patrickmcm/Alevel_RFID_Card_Reader/frontend/images/dashboard/img_1.jpg

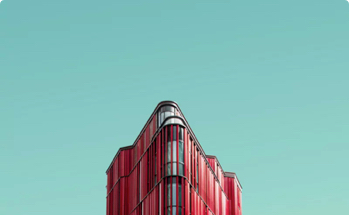
frontend/images/dashboard/img_1.jpg
