patrickmcm/Alevel_RFID_Card_Reader/frontend/images/auth/login-bg.jpg

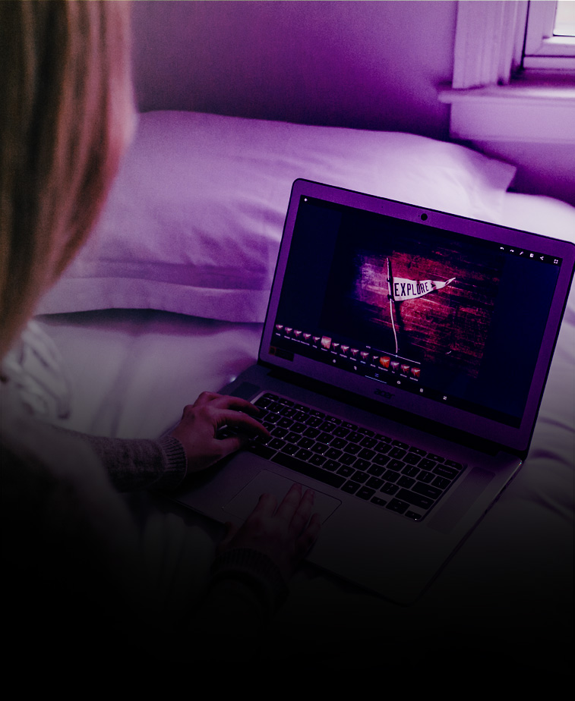
frontend/images/auth/login-bg.jpg
