patrickmcm/Alevel_RFID_Card_Reader/frontend/images/auth/lockscreen-bg.jpg

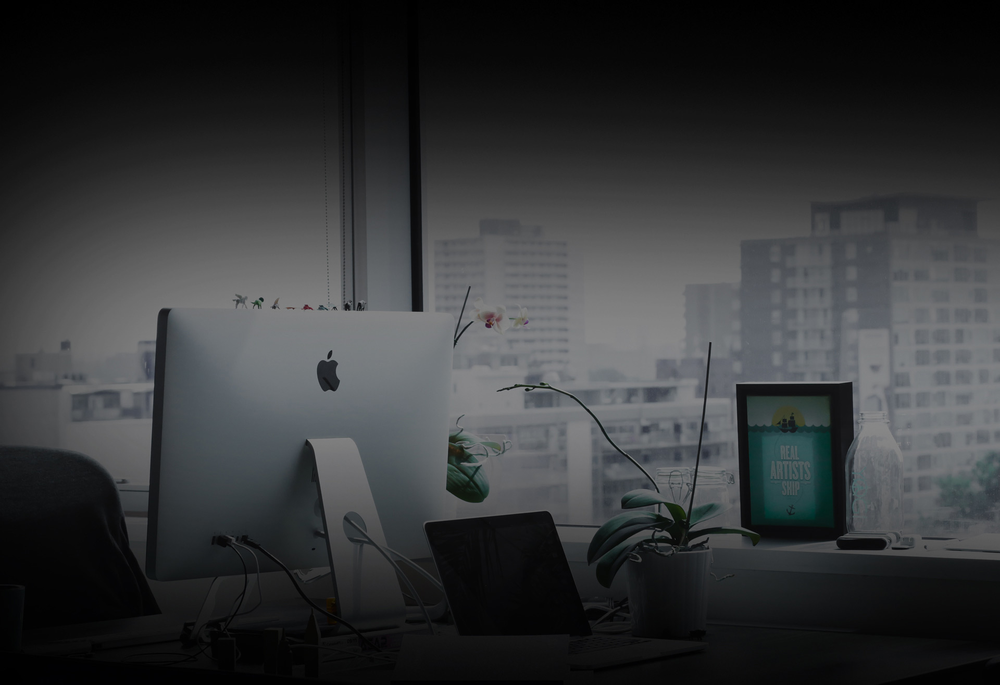
frontend/images/auth/lockscreen-bg.jpg
