patrickmcm/Alevel_RFID_Card_Reader/frontend/images/auth/register-bg.jpg

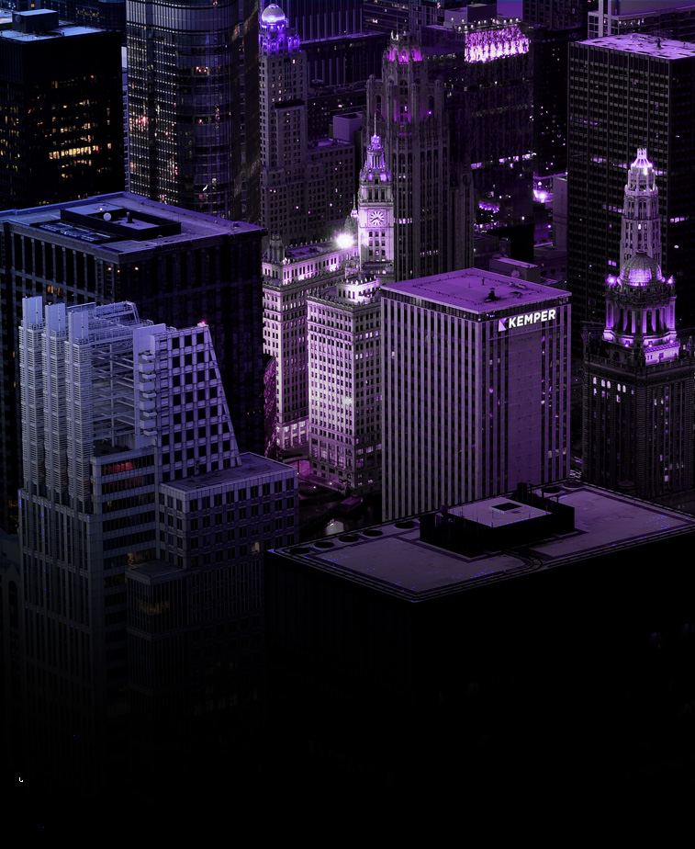
frontend/images/auth/register-bg.jpg
