patrickmcm/Alevel_RFID_Card_Reader/frontend/images/dashboard/darkBG.png

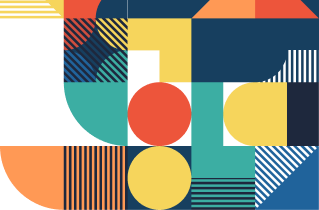
frontend/images/dashboard/darkBG.png
