patrickmcm/Alevel_RFID_Card_Reader/frontend/images/dashboard/img_2.jpg

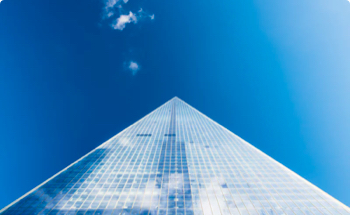
frontend/images/dashboard/img_2.jpg
