patrickmcm/Alevel_RFID_Card_Reader/frontend/images/dashboard/img_3.jpg

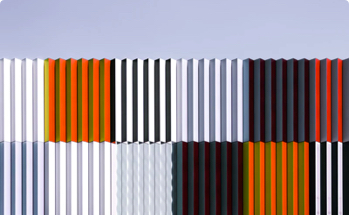
frontend/images/dashboard/img_3.jpg
