patrickmcm/Alevel_RFID_Card_Reader/frontend/images/dashboard/profile-card.jpg

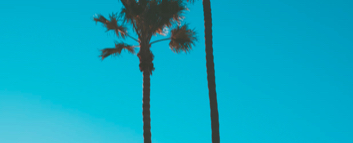
frontend/images/dashboard/profile-card.jpg
