patrickmcm/Alevel_RFID_Card_Reader/frontend/images/dashboard/progress-card-bg.jpg

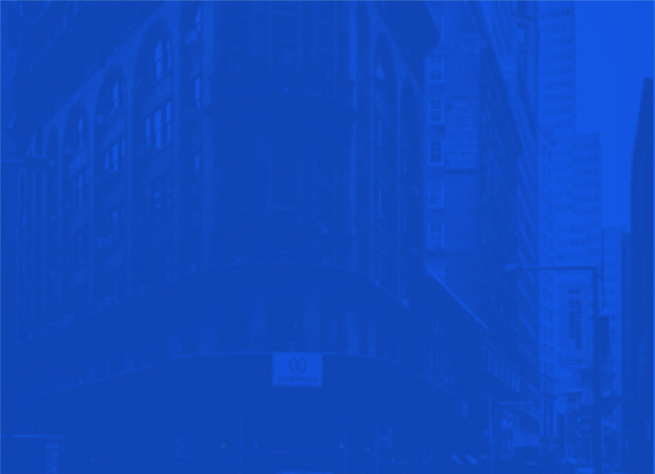
frontend/images/dashboard/progress-card-bg.jpg
