patrickmcm/Alevel_RFID_Card_Reader/frontend/images/dashboard/weather-card.jpg

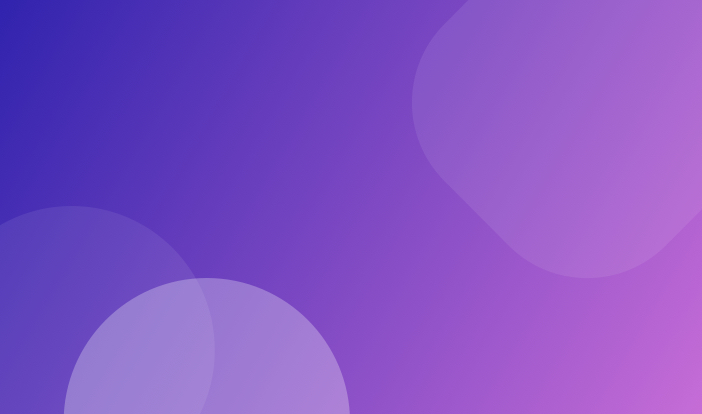
frontend/images/dashboard/weather-card.jpg
