patrickmcm/Alevel_RFID_Card_Reader/frontend/images/faces/profile/profile.jpg

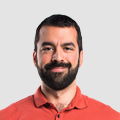
frontend/images/faces/profile/profile.jpg
