patrickmcm/Alevel_RFID_Card_Reader/frontend/images/lightbox/thumb-v-v-1.jpg

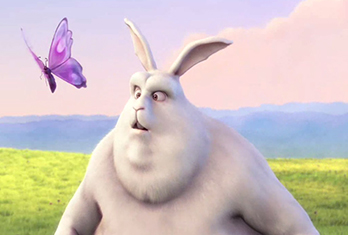
frontend/images/lightbox/thumb-v-v-1.jpg
