patrickmcm/Alevel_RFID_Card_Reader/frontend/images/lightbox/thumb-v-y-1.jpg

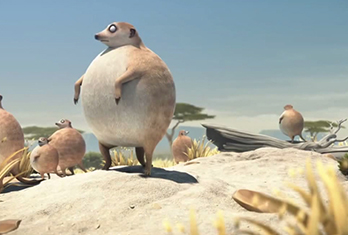
frontend/images/lightbox/thumb-v-y-1.jpg
