patrickmcm/Alevel_RFID_Card_Reader/frontend/images/lightbox/thumb-v-y-2.jpg

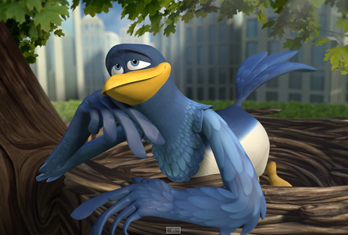
frontend/images/lightbox/thumb-v-y-2.jpg
