patrickmcm/Alevel_RFID_Card_Reader/hardware/schematic/schematic.kicad_sch

## KiCad design hardware/schematic/schematic.kicad_sch (2023-08-01)

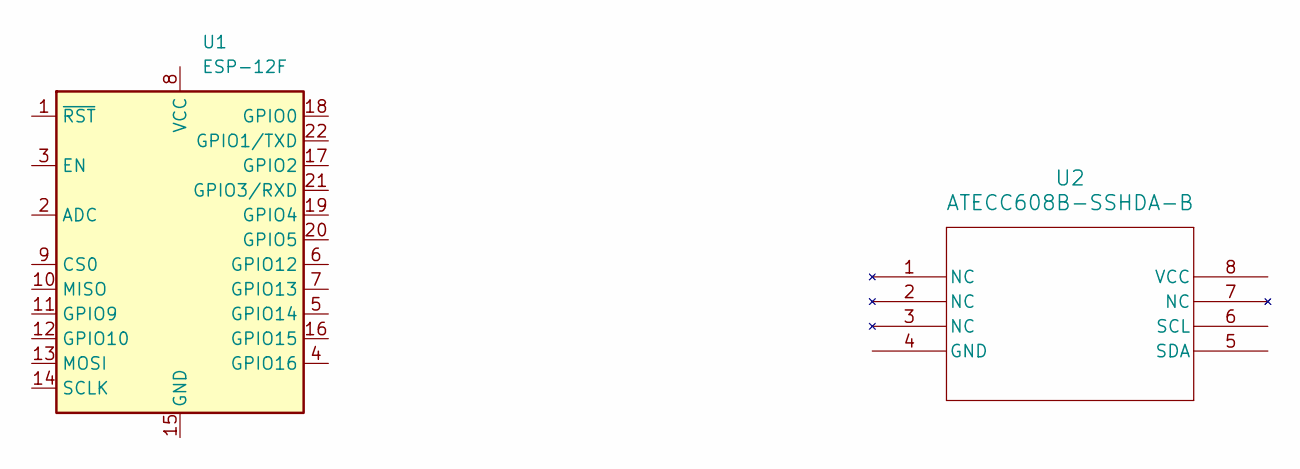
[picture p47: schematic schematic.kicad_sch]

Parts:
U1: ESP-12F; ESP-12E
U2: ATECC608B-SSHDA-B; SOIC8_NARROW_SN_MCH
